ymilord/Solidoodle-Press-E3D-v6/Parts/Direct/Press/Non_Bowden_PTFE_Example.jpg

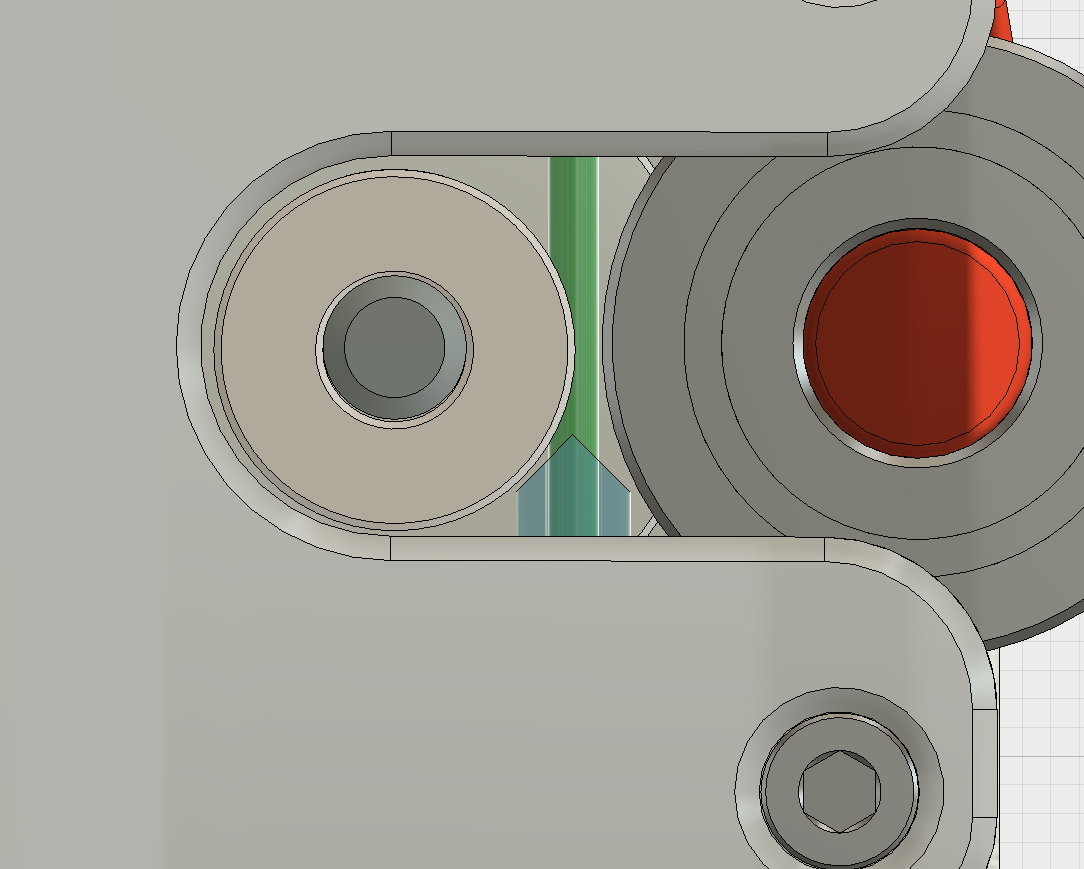
Parts/Direct/Press/Non_Bowden_PTFE_Example.jpg
