ymilord/Solidoodle-Press-E3D-v6/Parts/Direct/SD2/Standard/SD2_Non-Bowden_E3D_v6_Mount.jpg

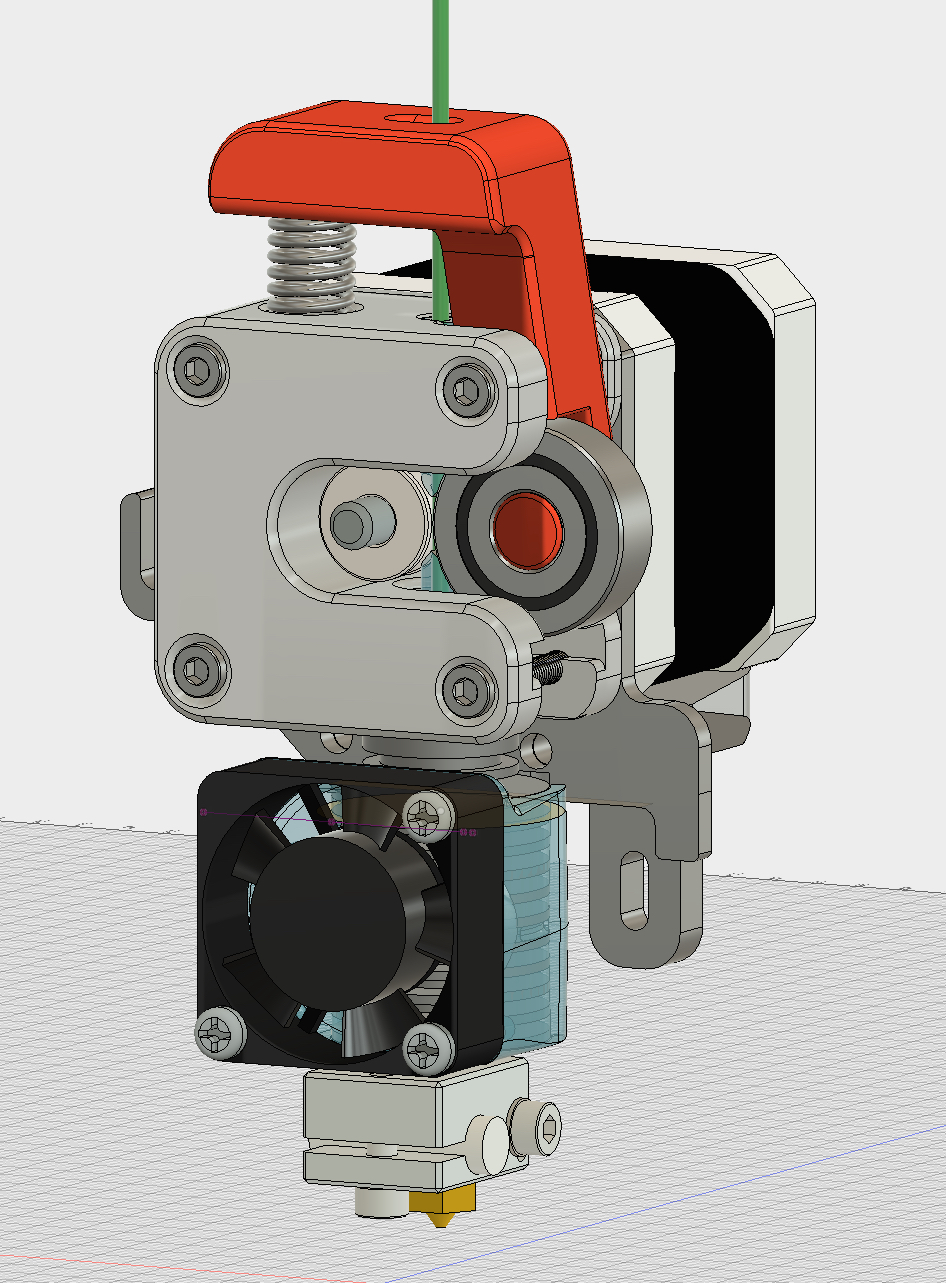
Parts/Direct/SD2/Standard/SD2_Non-Bowden_E3D_v6_Mount.jpg
