ymilord/Solidoodle-Press-E3D-v6/Parts/Press Fan Mount/Press_Stock_Fan_Mount.jpg

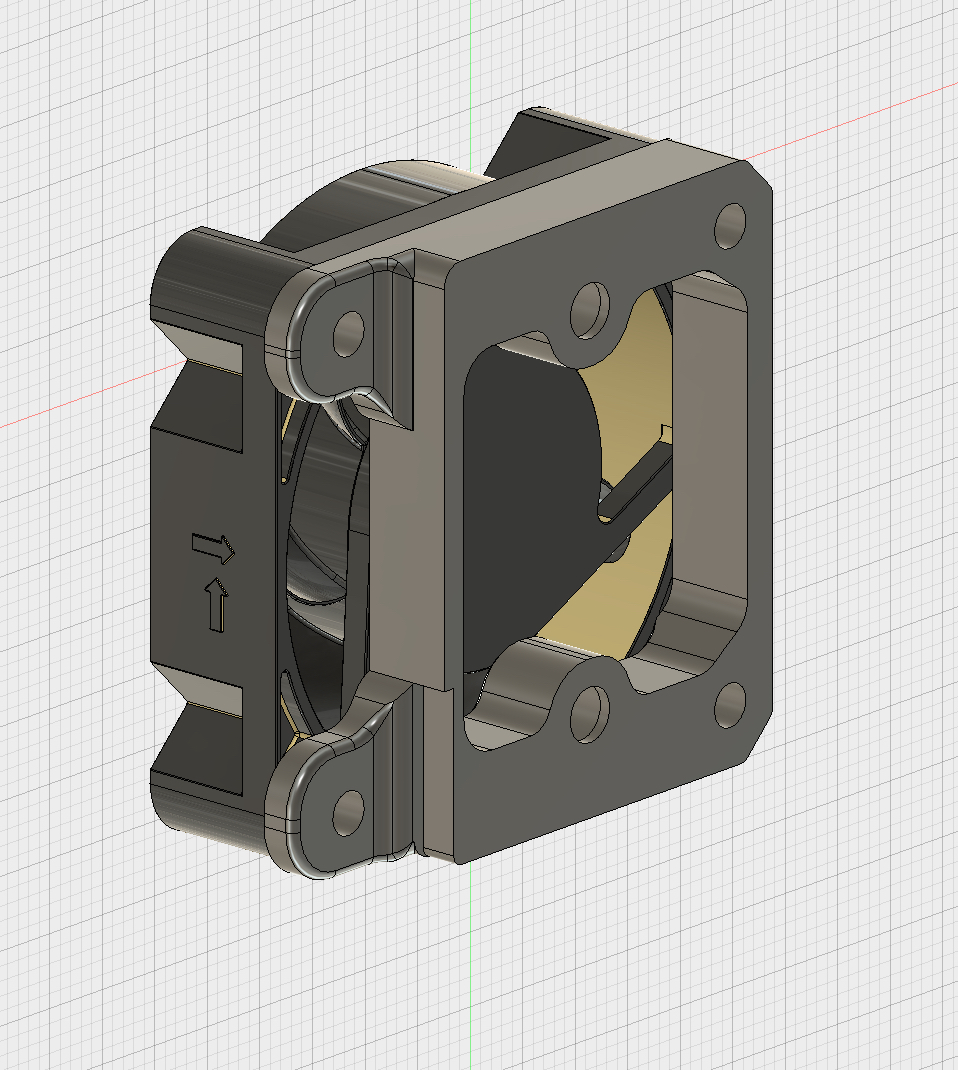
Parts/Press Fan Mount/Press_Stock_Fan_Mount.jpg
