ymilord/Solidoodle-Press-E3D-v6/Parts/Bowden/STL/Bowden_Lever.stl

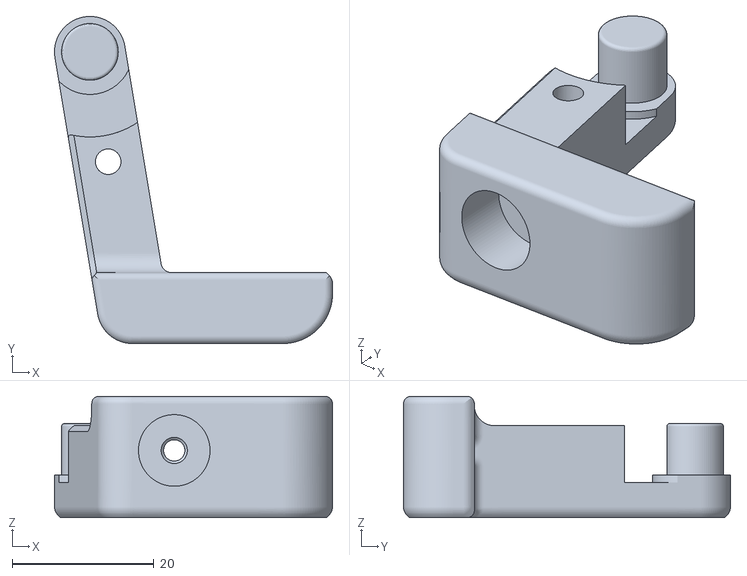
[picture p24: CAD file, 2015-02-19]
Parts/Bowden/STL/Bowden_Lever.stl
39.2 x 46.2 x 17.1
