ymilord/Solidoodle-Press-E3D-v6/Parts/Cyclops Parts/Left_Side_Shoe.stl

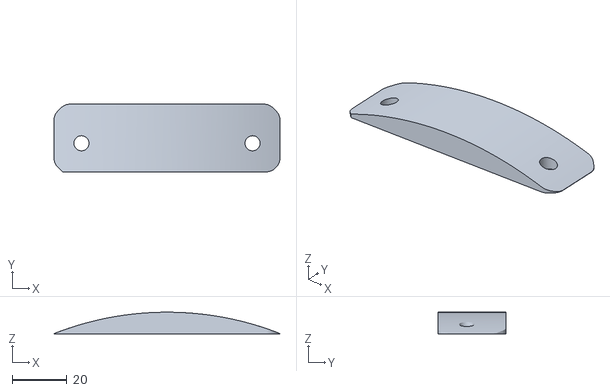
[picture p25: CAD file, 2015-06-15]
Parts/Cyclops Parts/Left_Side_Shoe.stl
82.3 x 24.7 x 7.88
