ymilord/Solidoodle-Press-E3D-v6/Parts/Cyclops Parts/Cyclops_Press_Mount.stl

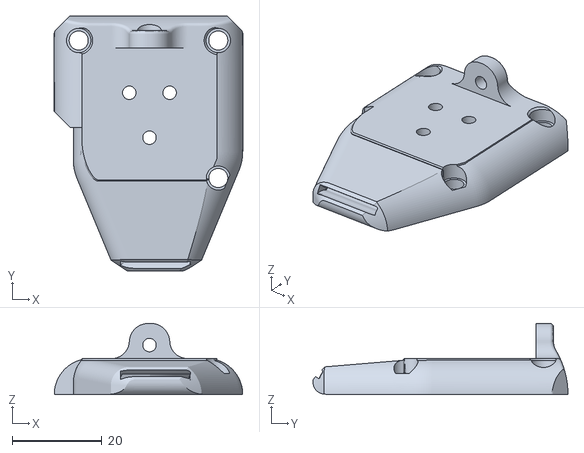
[picture p26: CAD file, 2015-06-15]
Parts/Cyclops Parts/Cyclops_Press_Mount.stl
42.0 x 56.8 x 15.9
