ymilord/Solidoodle-Press-E3D-v6/Parts/Bowden/E3D_v6_Bowden_Assembly.jpg

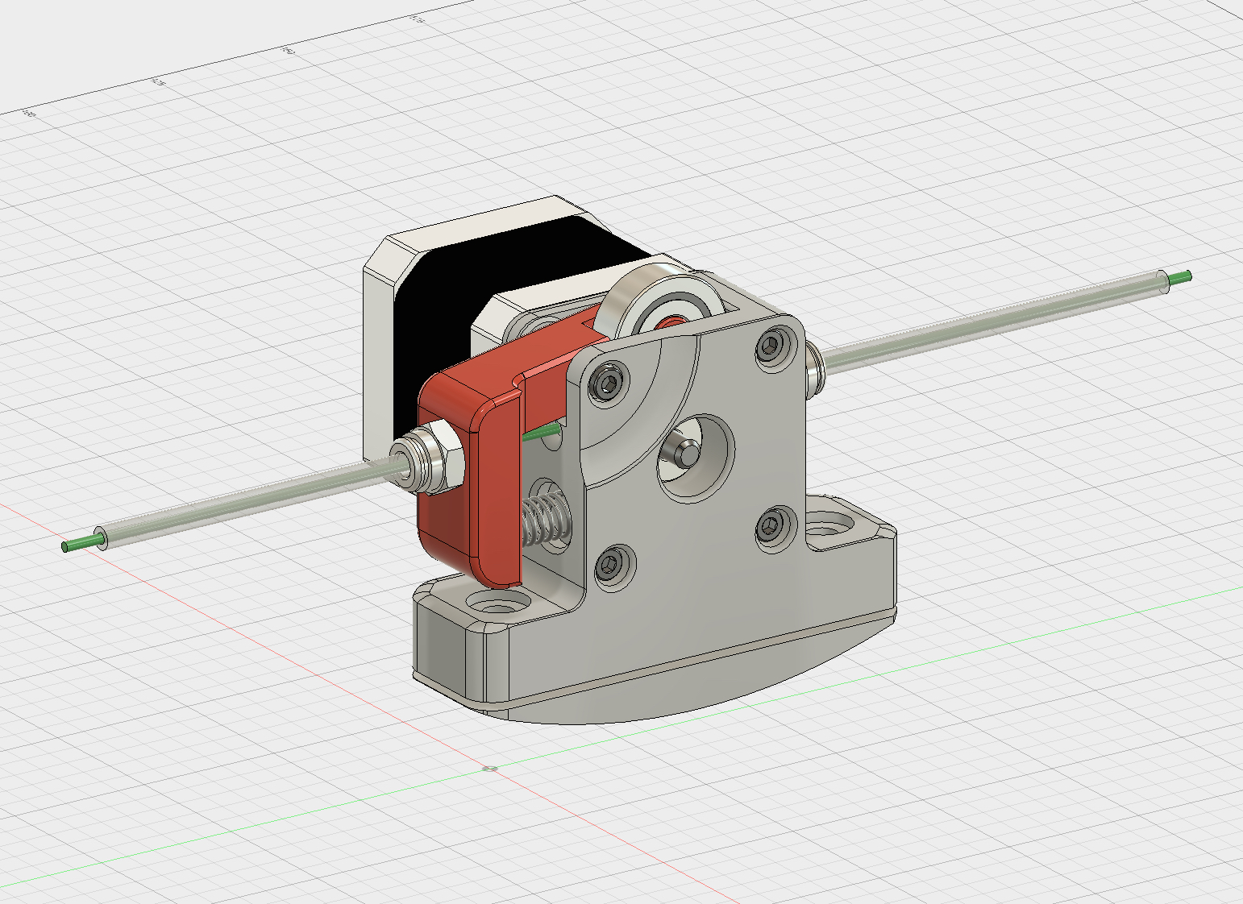
Parts/Bowden/E3D_v6_Bowden_Assembly.jpg
